somhi/DECA_retro_cape_1/datasheets-references/Atlas_ps2_2_usb.png

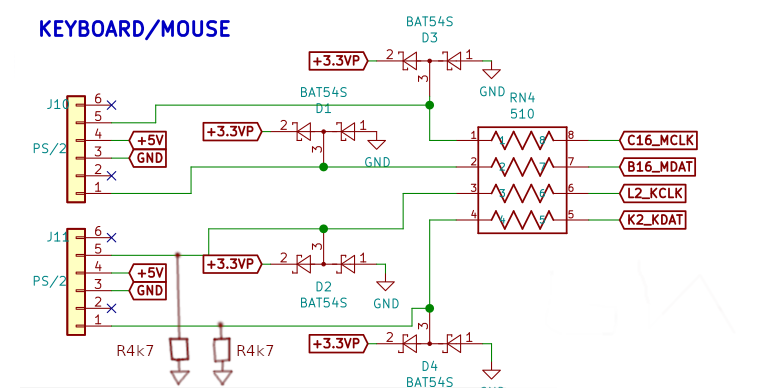
datasheets-references/Atlas_ps2_2_usb.png
