somhi/DECA_retro_cape_1/datasheets-references/db9-sega.png

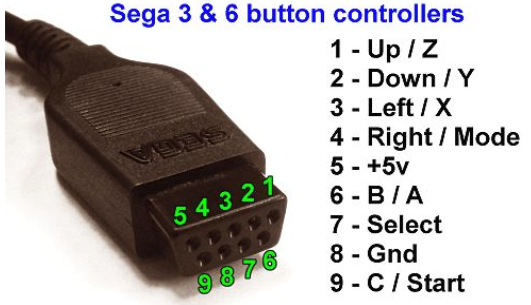
datasheets-references/db9-sega.png
