somhi/DECA_retro_cape_1/datasheets-references/DE10-Nano-mides.jpg

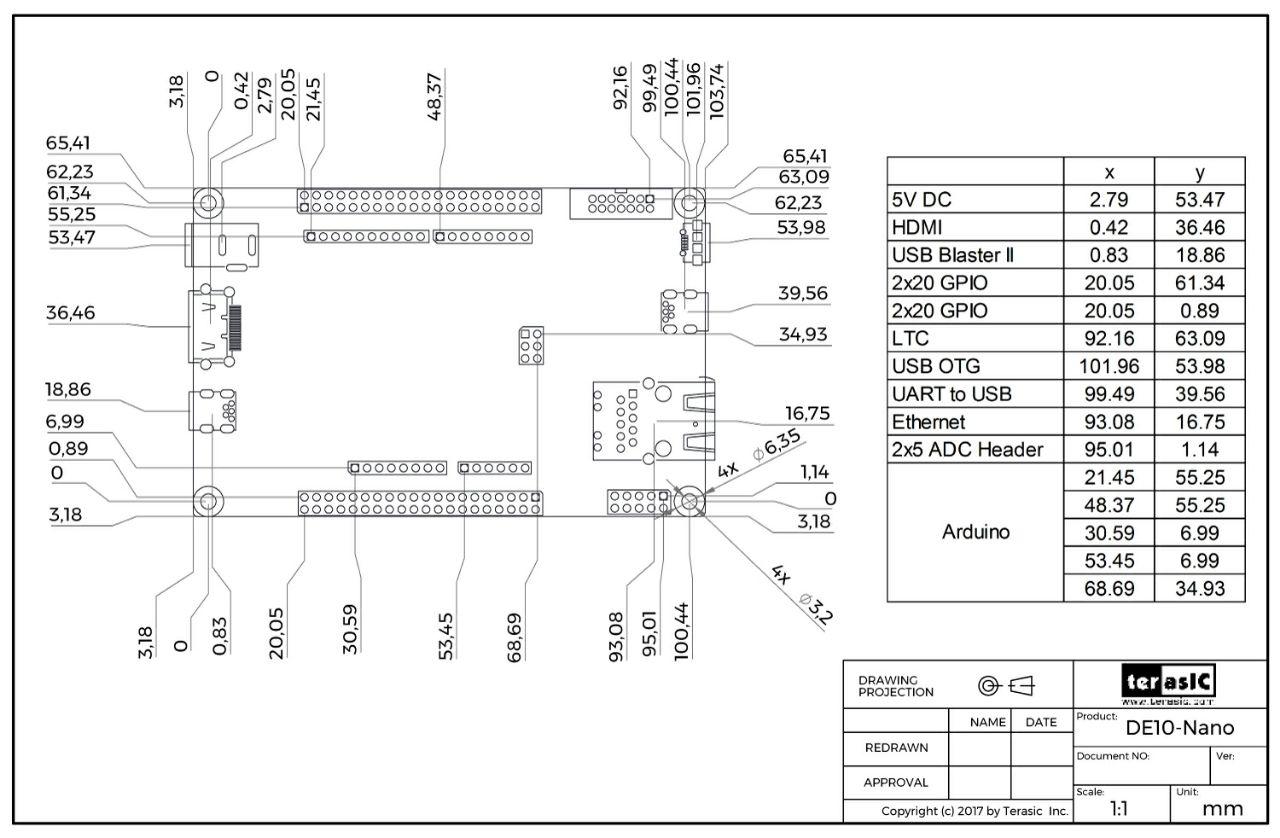
datasheets-references/DE10-Nano-mides.jpg
