somhi/DECA_retro_cape_1/datasheets-references/IO_board_for_MiSTer_r6.1.png

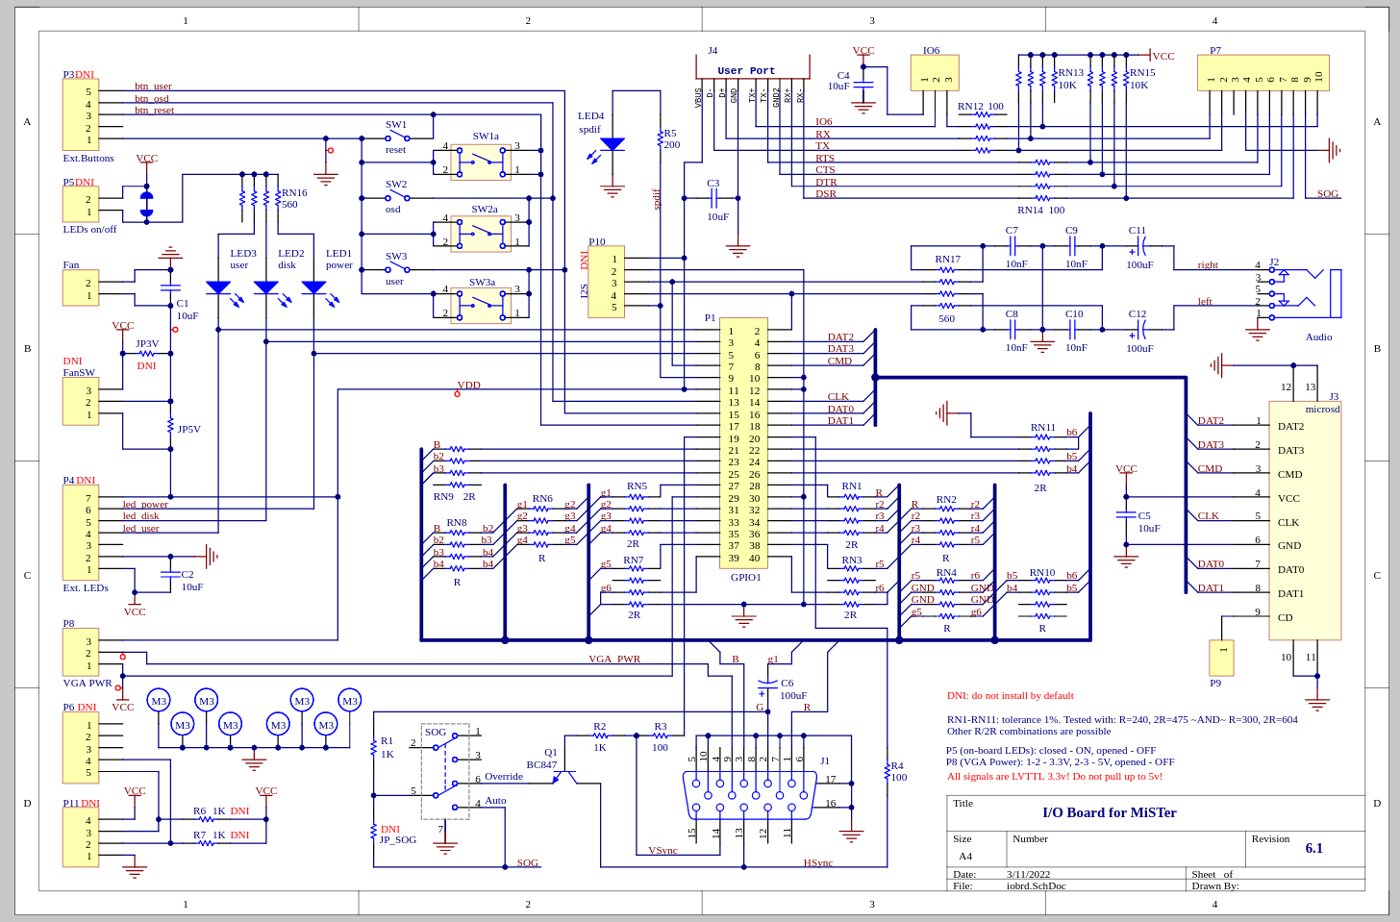
datasheets-references/IO_board_for_MiSTer_r6.1.png
