somhi/DECA_retro_cape_1/datasheets-references/pmod-vga-serigrafia-ok.jpg

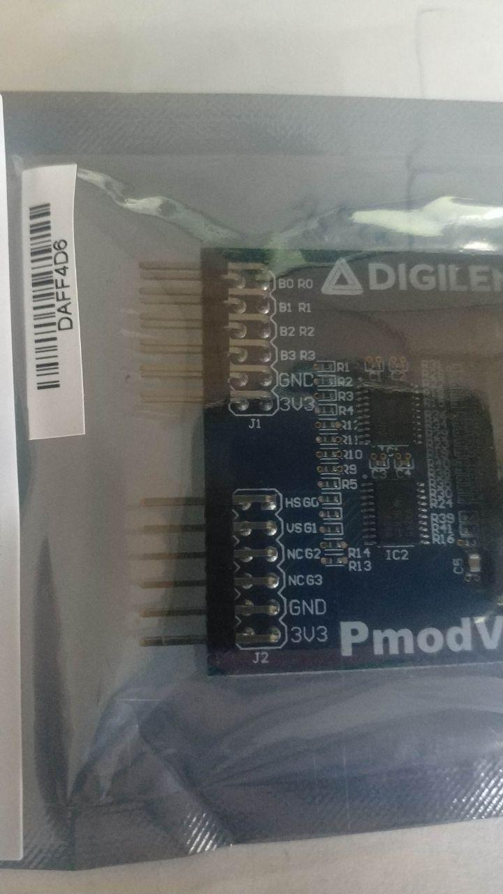
datasheets-references/pmod-vga-serigrafia-ok.jpg
